haykonus/JU-TE-6K-Video-HW-Patch/KiCAD/JU-TE-6K-Video-HW-Patch.kicad_sch

## KiCad design KiCAD/JU-TE-6K-Video-HW-Patch.kicad_sch (2024-06-11)

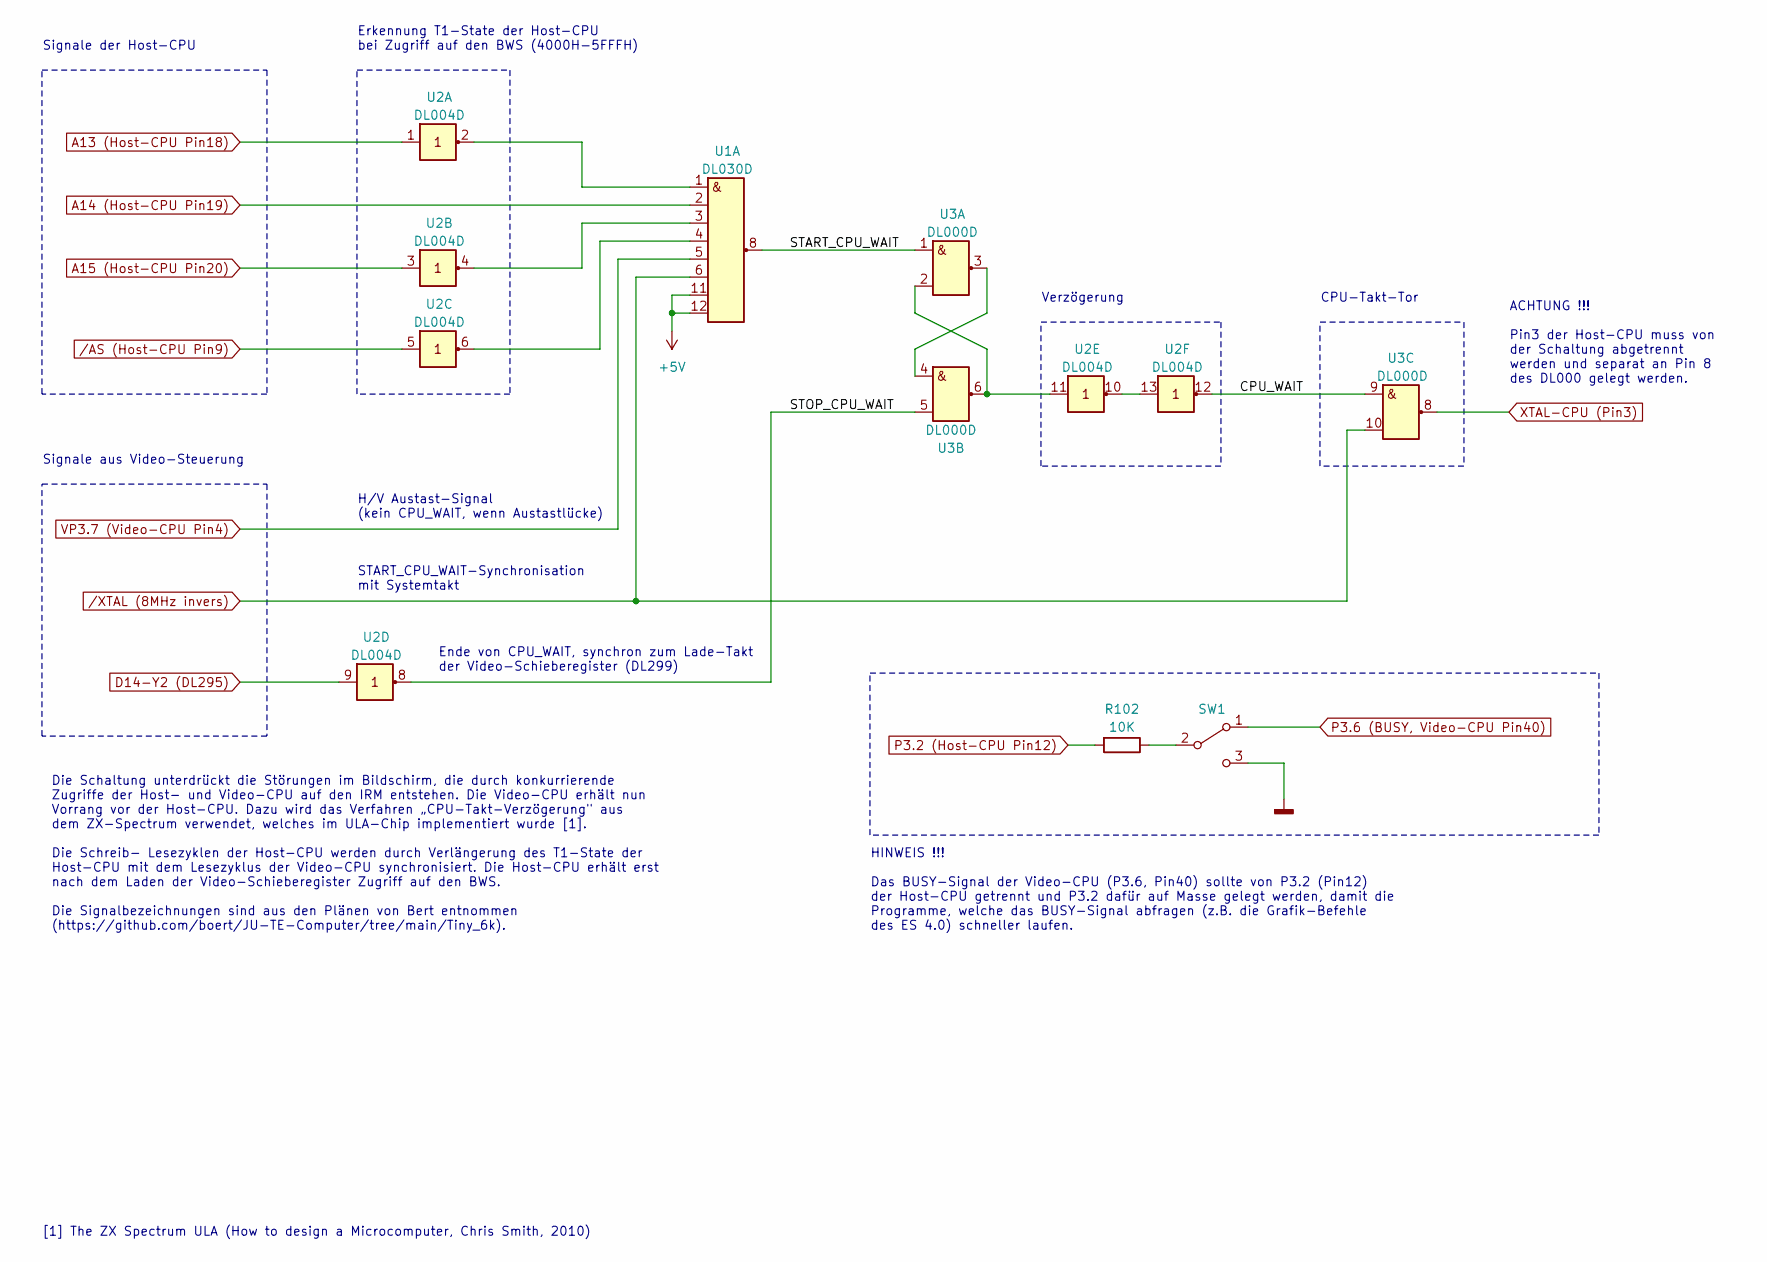
[picture p15: schematic JU-TE-6K-Video-HW-Patch.kicad_sch]

Parts:
R102: 10K
SW1: (no value)
U1: DL030D
U2: DL004D
U3: DL000D

Connections:
+5V: U1.11 (G), U1.12 (H)
A13 (Host-CPU Pin18): U2.1 (A1)
A14 (Host-CPU Pin19): U1.2 (B)
A15 (Host-CPU Pin20): U2.3 (A2)
CPU_WAIT: U2.12 (Y6), U3.9 (A3)
D14-Y2 (DL295): U2.9 (A4)
GNDD: SW1.3 (C)
unnamed: R102.1, SW1.2 (B)
unnamed: U1.1 (A), U2.2 (Y1)
unnamed: U1.3 (C), U2.4 (Y2)
unnamed: U1.4 (D), U2.6 (Y3)
unnamed: U2.10 (Y5), U2.13 (A6)
unnamed: U2.11 (A5), U3.2 (B1), U3.6 (Y2)
unnamed: U3.3 (Y1), U3.4 (A2)
P3.2 (Host-CPU Pin12): R102.2
P3.6 (BUSY, Video-CPU Pin40): SW1.1 (A)
START_CPU_WAIT: U1.8 (Y), U3.1 (A1)
STOP_CPU_WAIT: U2.8 (Y4), U3.5 (B2)
VP3.7 (Video-CPU Pin4): U1.5 (E)
XTAL-CPU (Pin3): U3.8 (Y3)
/AS (Host-CPU Pin9): U2.5 (A3)
/XTAL (8MHz invers): U1.6 (F), U3.10 (B3)

Notes on the sheet:
ACHTUNG !!! Pin3 der Host-CPU muss von der Schaltung abgetrennt werden und separat an Pin 8 des DL000 gelegt werden.
HINWEIS !!! Das BUSY-Signal der Video-CPU (P3.6, Pin40) sollte von P3.2 (Pin12) der Host-CPU getrennt und P3.2 dafür auf Masse gelegt werden, damit die Programme, welche das BUSY-Signal abfragen (z.B. die Grafik-Befehle des ES 4.0) schneller laufen.
Die Schaltung unterdrückt die Störungen im Bildschirm, die durch konkurrierende Zugriffe der Host- und Video-CPU auf den IRM entstehen. Die Video-CPU erhält nun Vorrang vor der Host-CPU. Dazu wird das Verfahren „CPU-Takt-Verzögerung" aus dem ZX-Spectrum verwendet, welches im ULA-Chip implementiert 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
Erkennung T1-State der Host-CPU bei Zugriff auf den BWS (4000H-5FFFH)
[1] The ZX Spectrum ULA (How to design a Microcomputer, Chris Smith, 2010)
H/V Austast-Signal (kein CPU_WAIT, wenn Austastlücke)
CPU-Takt-Tor
Signale aus Video-Steuerung
Signale der Host-CPU
Ende von CPU_WAIT, synchron zum Lade-Takt der Video-Schieberegister (DL299)
START_CPU_WAIT-Synchronisation mit Systemtakt
Verzögerung
