haykonus/JU-TE-6K-Video-HW-Patch/KiCAD/JU-TE-6K-Video-Patch.kicad_sch

## KiCad design KiCAD/JU-TE-6K-Video-Patch.kicad_sch (2024-05-16)

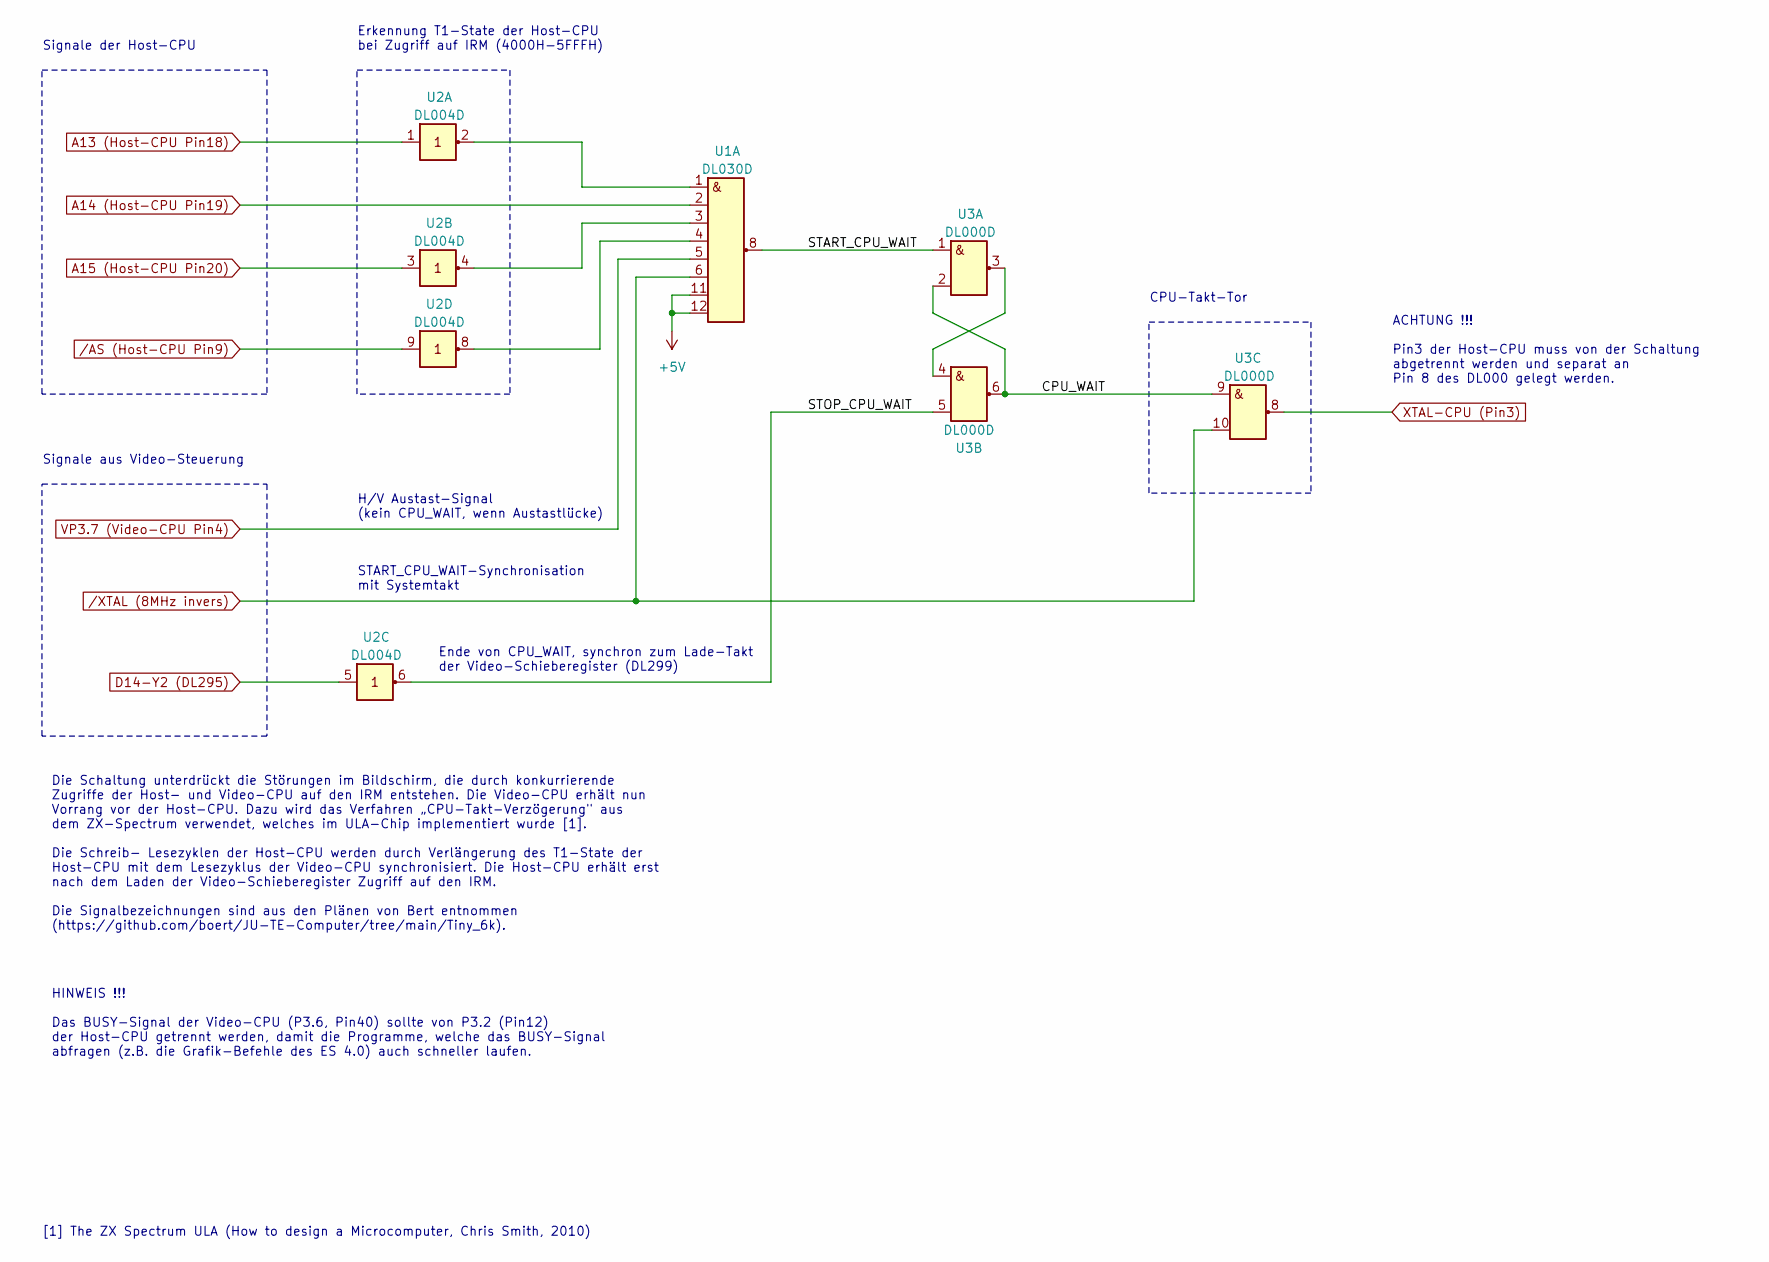
[picture p16: schematic JU-TE-6K-Video-Patch.kicad_sch]

Parts:
U1: DL030D
U2: DL004D
U3: DL000D

Connections:
+5V: U1.11 (G), U1.12 (H)
A13 (Host-CPU Pin18): U2.1 (A1)
A14 (Host-CPU Pin19): U1.2 (B)
A15 (Host-CPU Pin20): U2.3 (A2)
CPU_WAIT: U3.2 (B1), U3.6 (Y2), U3.9 (A3)
D14-Y2 (DL295): U2.5 (A3)
unnamed: U1.1 (A), U2.2 (Y1)
unnamed: U1.3 (C), U2.4 (Y2)
unnamed: U1.4 (D), U2.8 (Y4)
unnamed: U3.3 (Y1), U3.4 (A2)
START_CPU_WAIT: U1.8 (Y), U3.1 (A1)
STOP_CPU_WAIT: U2.6 (Y3), U3.5 (B2)
VP3.7 (Video-CPU Pin4): U1.5 (E)
XTAL-CPU (Pin3): U3.8 (Y3)
/AS (Host-CPU Pin9): U2.9 (A4)
/XTAL (8MHz invers): U1.6 (F), U3.10 (B3)

Notes on the sheet:
ACHTUNG !!! Pin3 der Host-CPU muss von der Schaltung abgetrennt werden und separat an Pin 8 des DL000 gelegt werden.
HINWEIS !!! Das BUSY-Signal der Video-CPU (P3.6, Pin40) sollte von P3.2 (Pin12) der Host-CPU getrennt werden, damit die Programme, welche das BUSY-Signal abfragen (z.B. die Grafik-Befehle des ES 4.0) auch schneller laufen.
Die Schaltung unterdrückt die Störungen im Bildschirm, die durch konkurrierende Zugriffe der Host- und Video-CPU auf den IRM entstehen. Die Video-CPU erhält nun Vorrang vor der Host-CPU. Dazu wird das Verfahren „CPU-Takt-Verzögerung" aus dem ZX-Spectrum verwendet, welches im ULA-Chip implementiert 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
Erkennung T1-State der Host-CPU bei Zugriff auf IRM (4000H-5FFFH)
[1] The ZX Spectrum ULA (How to design a Microcomputer, Chris Smith, 2010)
H/V Austast-Signal (kein CPU_WAIT, wenn Austastlücke)
CPU-Takt-Tor
Signale aus Video-Steuerung
Signale der Host-CPU
Ende von CPU_WAIT, synchron zum Lade-Takt der Video-Schieberegister (DL299)
START_CPU_WAIT-Synchronisation mit Systemtakt
